Aymane-Rehahla/Industrial-Monitoring-Protection-Predictive-Maintenance-Platform/hardware/photos/5953918394727861724.jpg

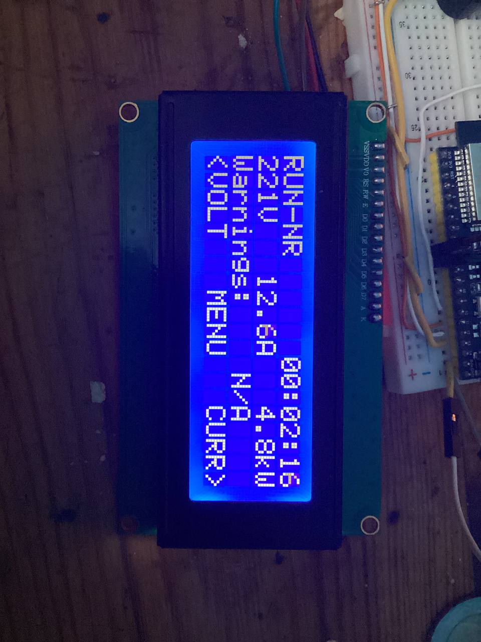
hardware/photos/5953918394727861724.jpg
