Aymane-Rehahla/Industrial-Monitoring-Protection-Predictive-Maintenance-Platform/hardware/photos/5976606971785841999.jpg

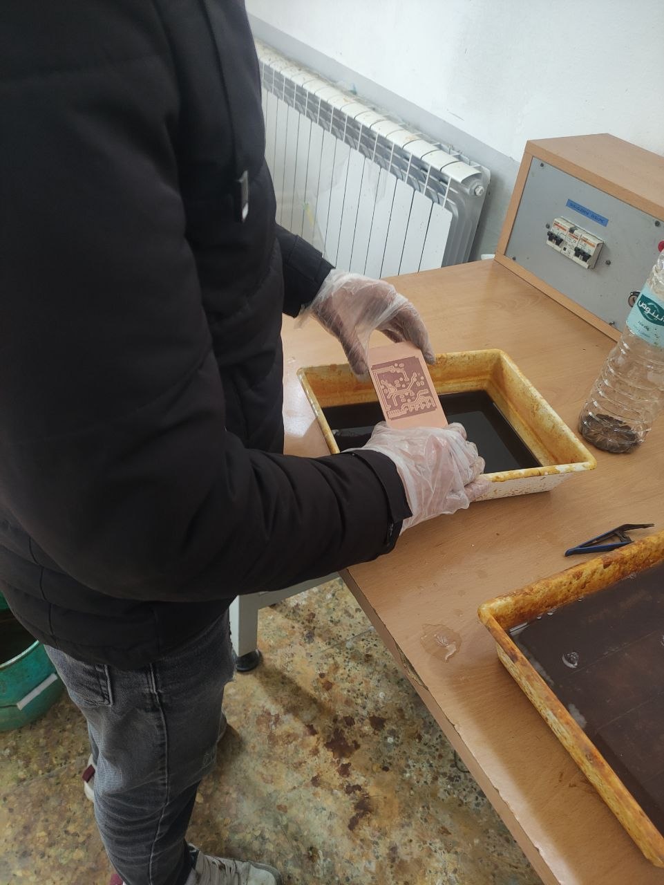
hardware/photos/5976606971785841999.jpg
