Aymane-Rehahla/Industrial-Monitoring-Protection-Predictive-Maintenance-Platform/hardware/photos/5985752456102611955.jpg

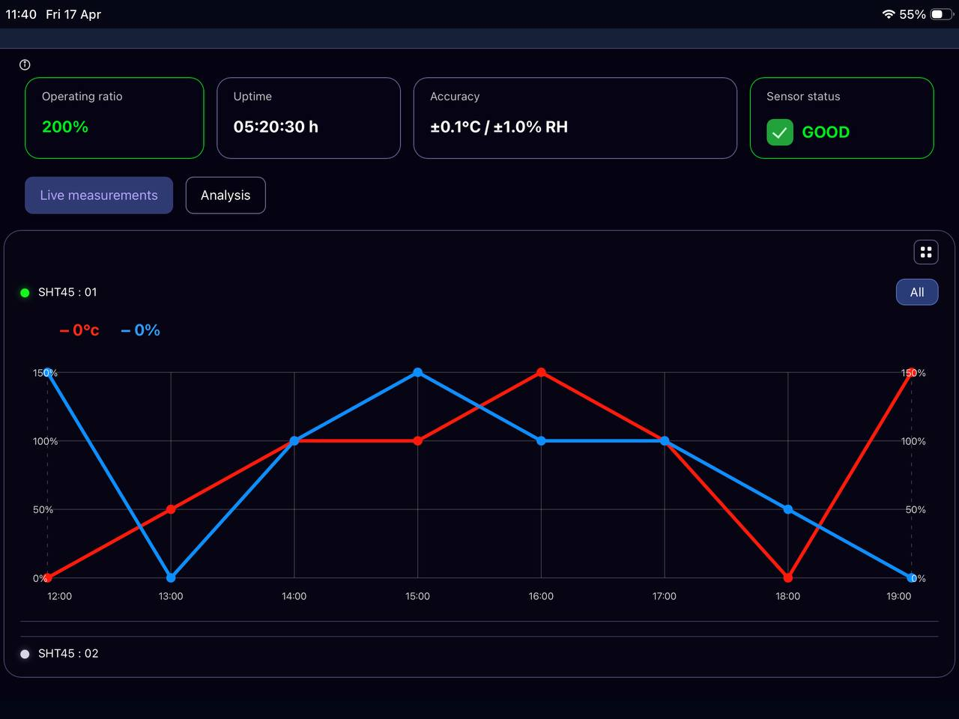
hardware/photos/5985752456102611955.jpg
