Aymane-Rehahla/Industrial-Monitoring-Protection-Predictive-Maintenance-Platform/hardware/photos/5985752456102612090.jpg

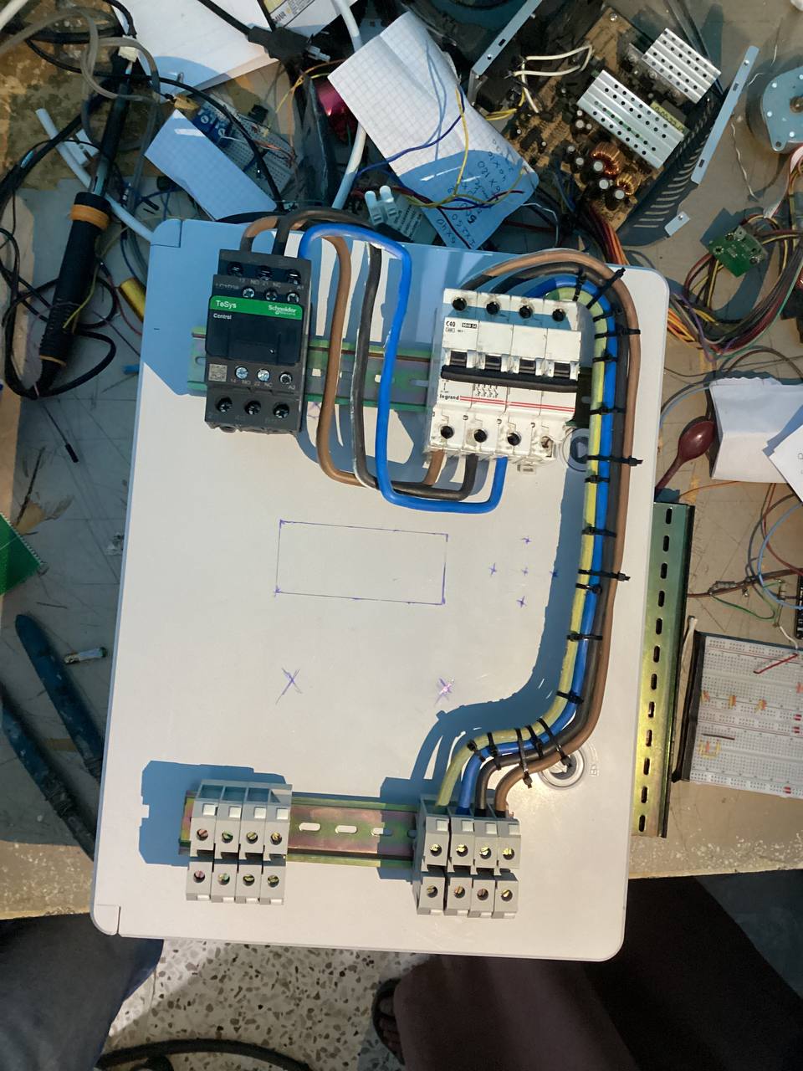
hardware/photos/5985752456102612090.jpg
