Aymane-Rehahla/Industrial-Monitoring-Protection-Predictive-Maintenance-Platform/hardware/photos/5990224212842450469.jpg

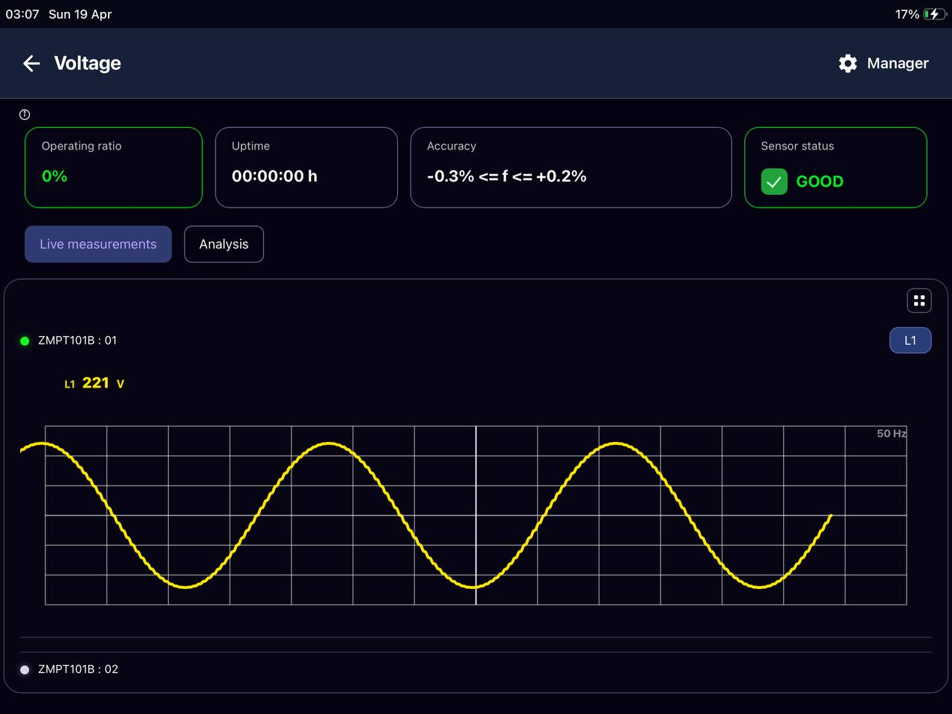
hardware/photos/5990224212842450469.jpg
