Aymane-Rehahla/Industrial-Monitoring-Protection-Predictive-Maintenance-Platform/hardware/photos/5994778415774501927.jpg

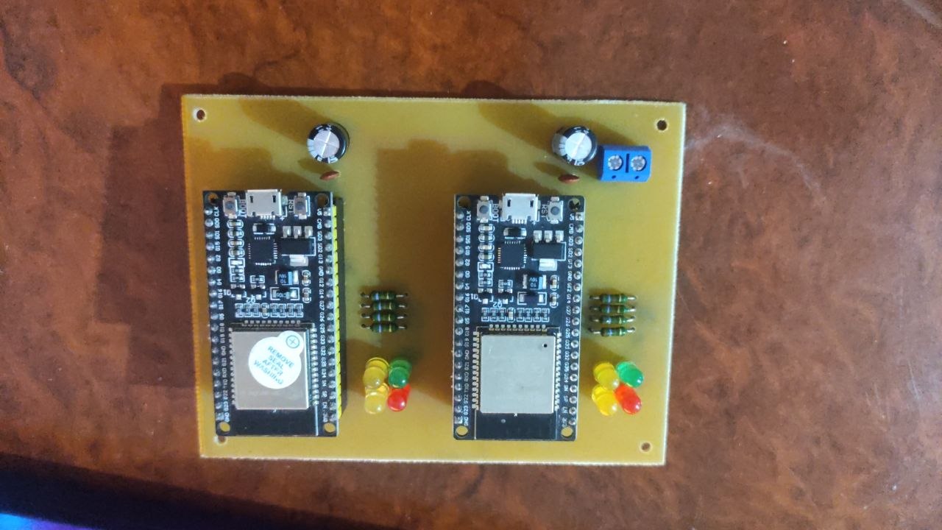
hardware/photos/5994778415774501927.jpg
