Aymane-Rehahla/Industrial-Monitoring-Protection-Predictive-Maintenance-Platform/hardware/photos/6046517803730275521.jpg

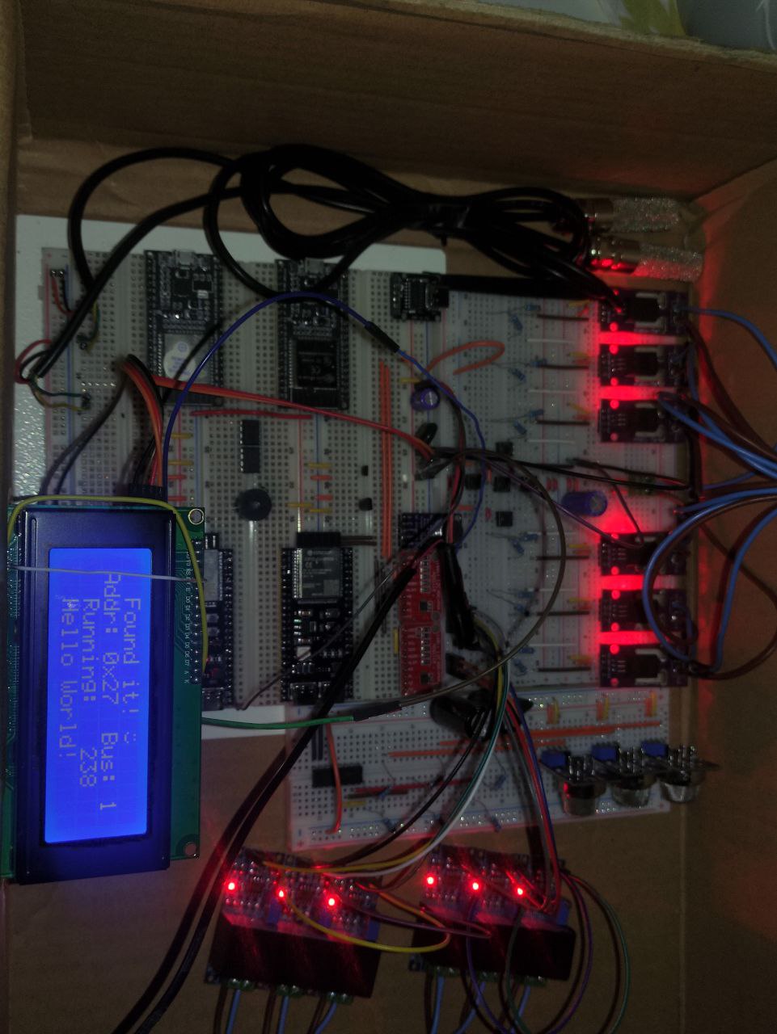
hardware/photos/6046517803730275521.jpg
