Aymane-Rehahla/Industrial-Monitoring-Protection-Predictive-Maintenance-Platform/hardware/photos/6050603846637129362.jpg

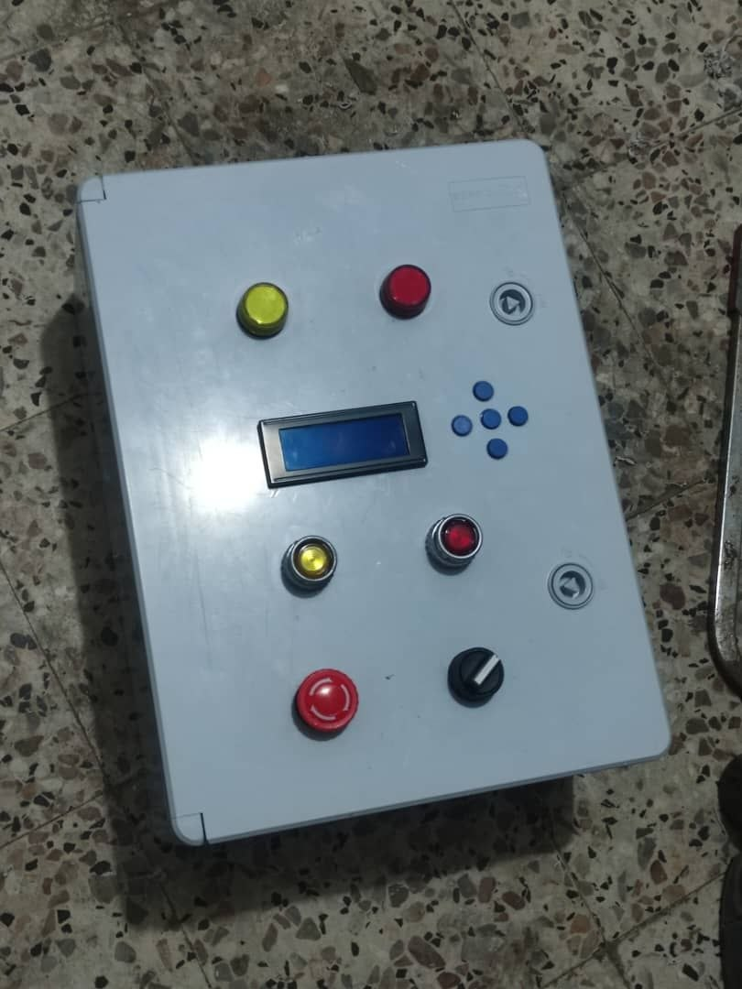
hardware/photos/6050603846637129362.jpg
