Aymane-Rehahla/Industrial-Monitoring-Protection-Predictive-Maintenance-Platform/firmware/Safty_Module-codebase/main/drivers/sensors/drv_current_sensor.h

#ifndef DRV_CURRENT_SENSOR_H
#define DRV_CURRENT_SENSOR_H

#include "system_types.h"
#include <stdint.h>

error_code_t drv_current_sensor_init(void);
error_code_t drv_current_sensor_read_phase(uint8_t phase,
                                           sensor_reading_t *out);

#endif
